Hypernova-Oy/lainuri/enclosures/KaskenPoltto.pdf

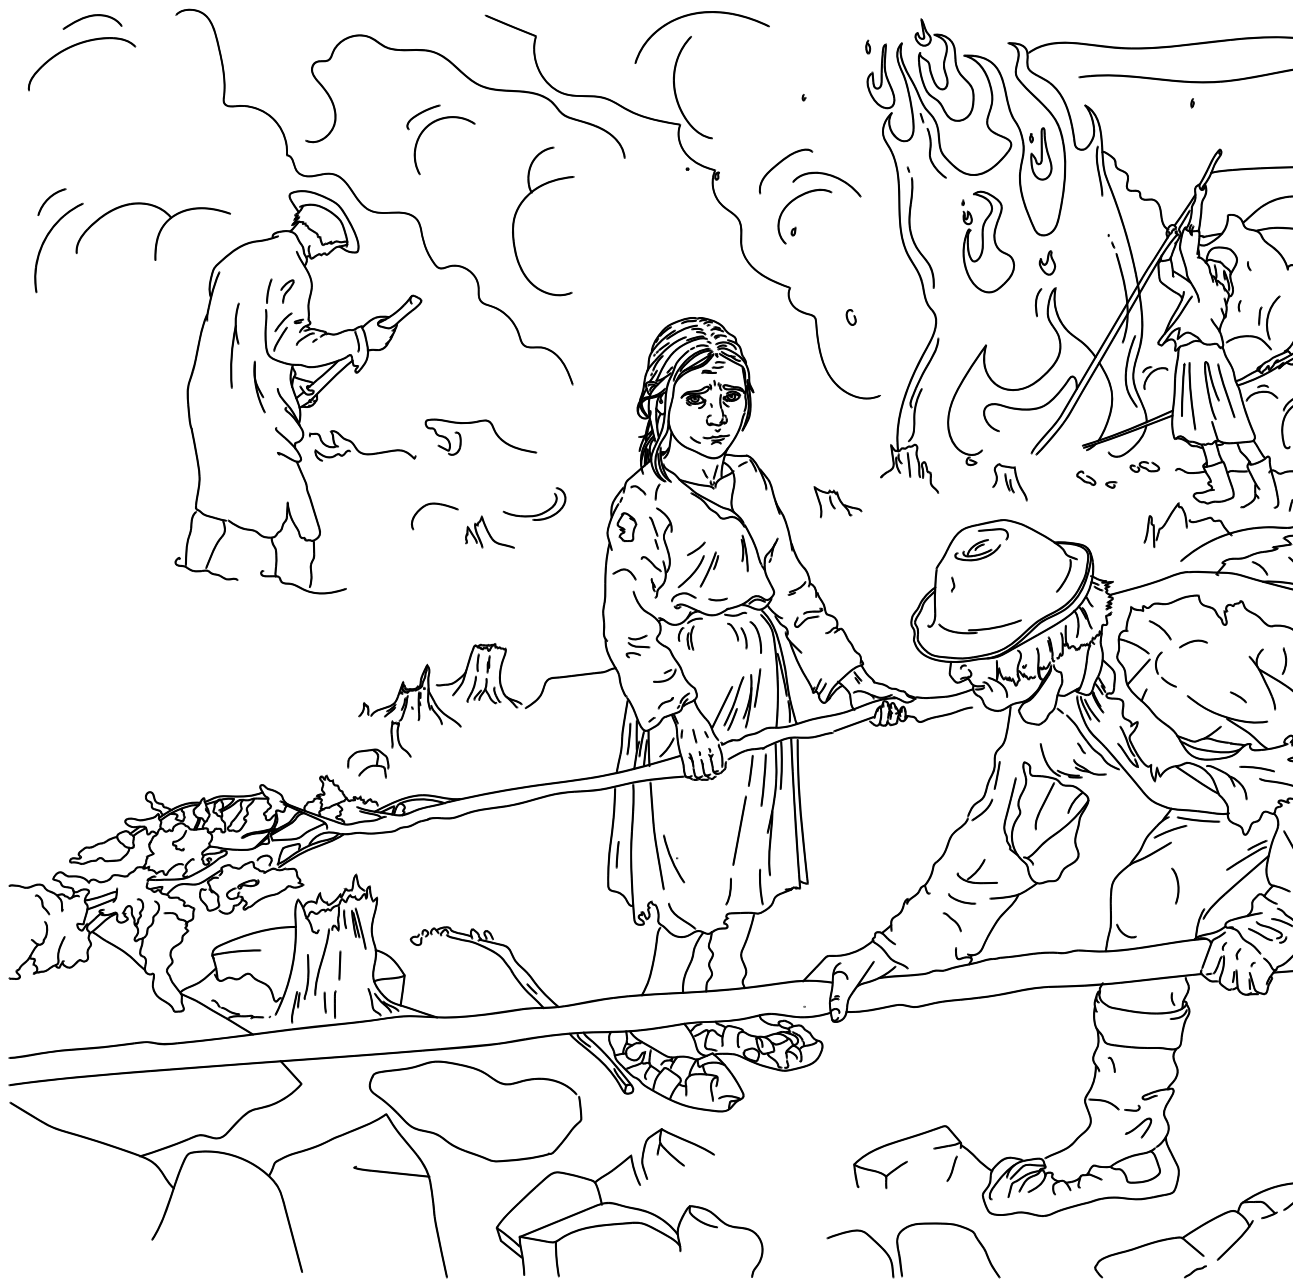
[picture p6: page 1]
