Hypernova-Oy/lainuri/enclosures/Lainuri-enclosure-4.5mm-art.pdf

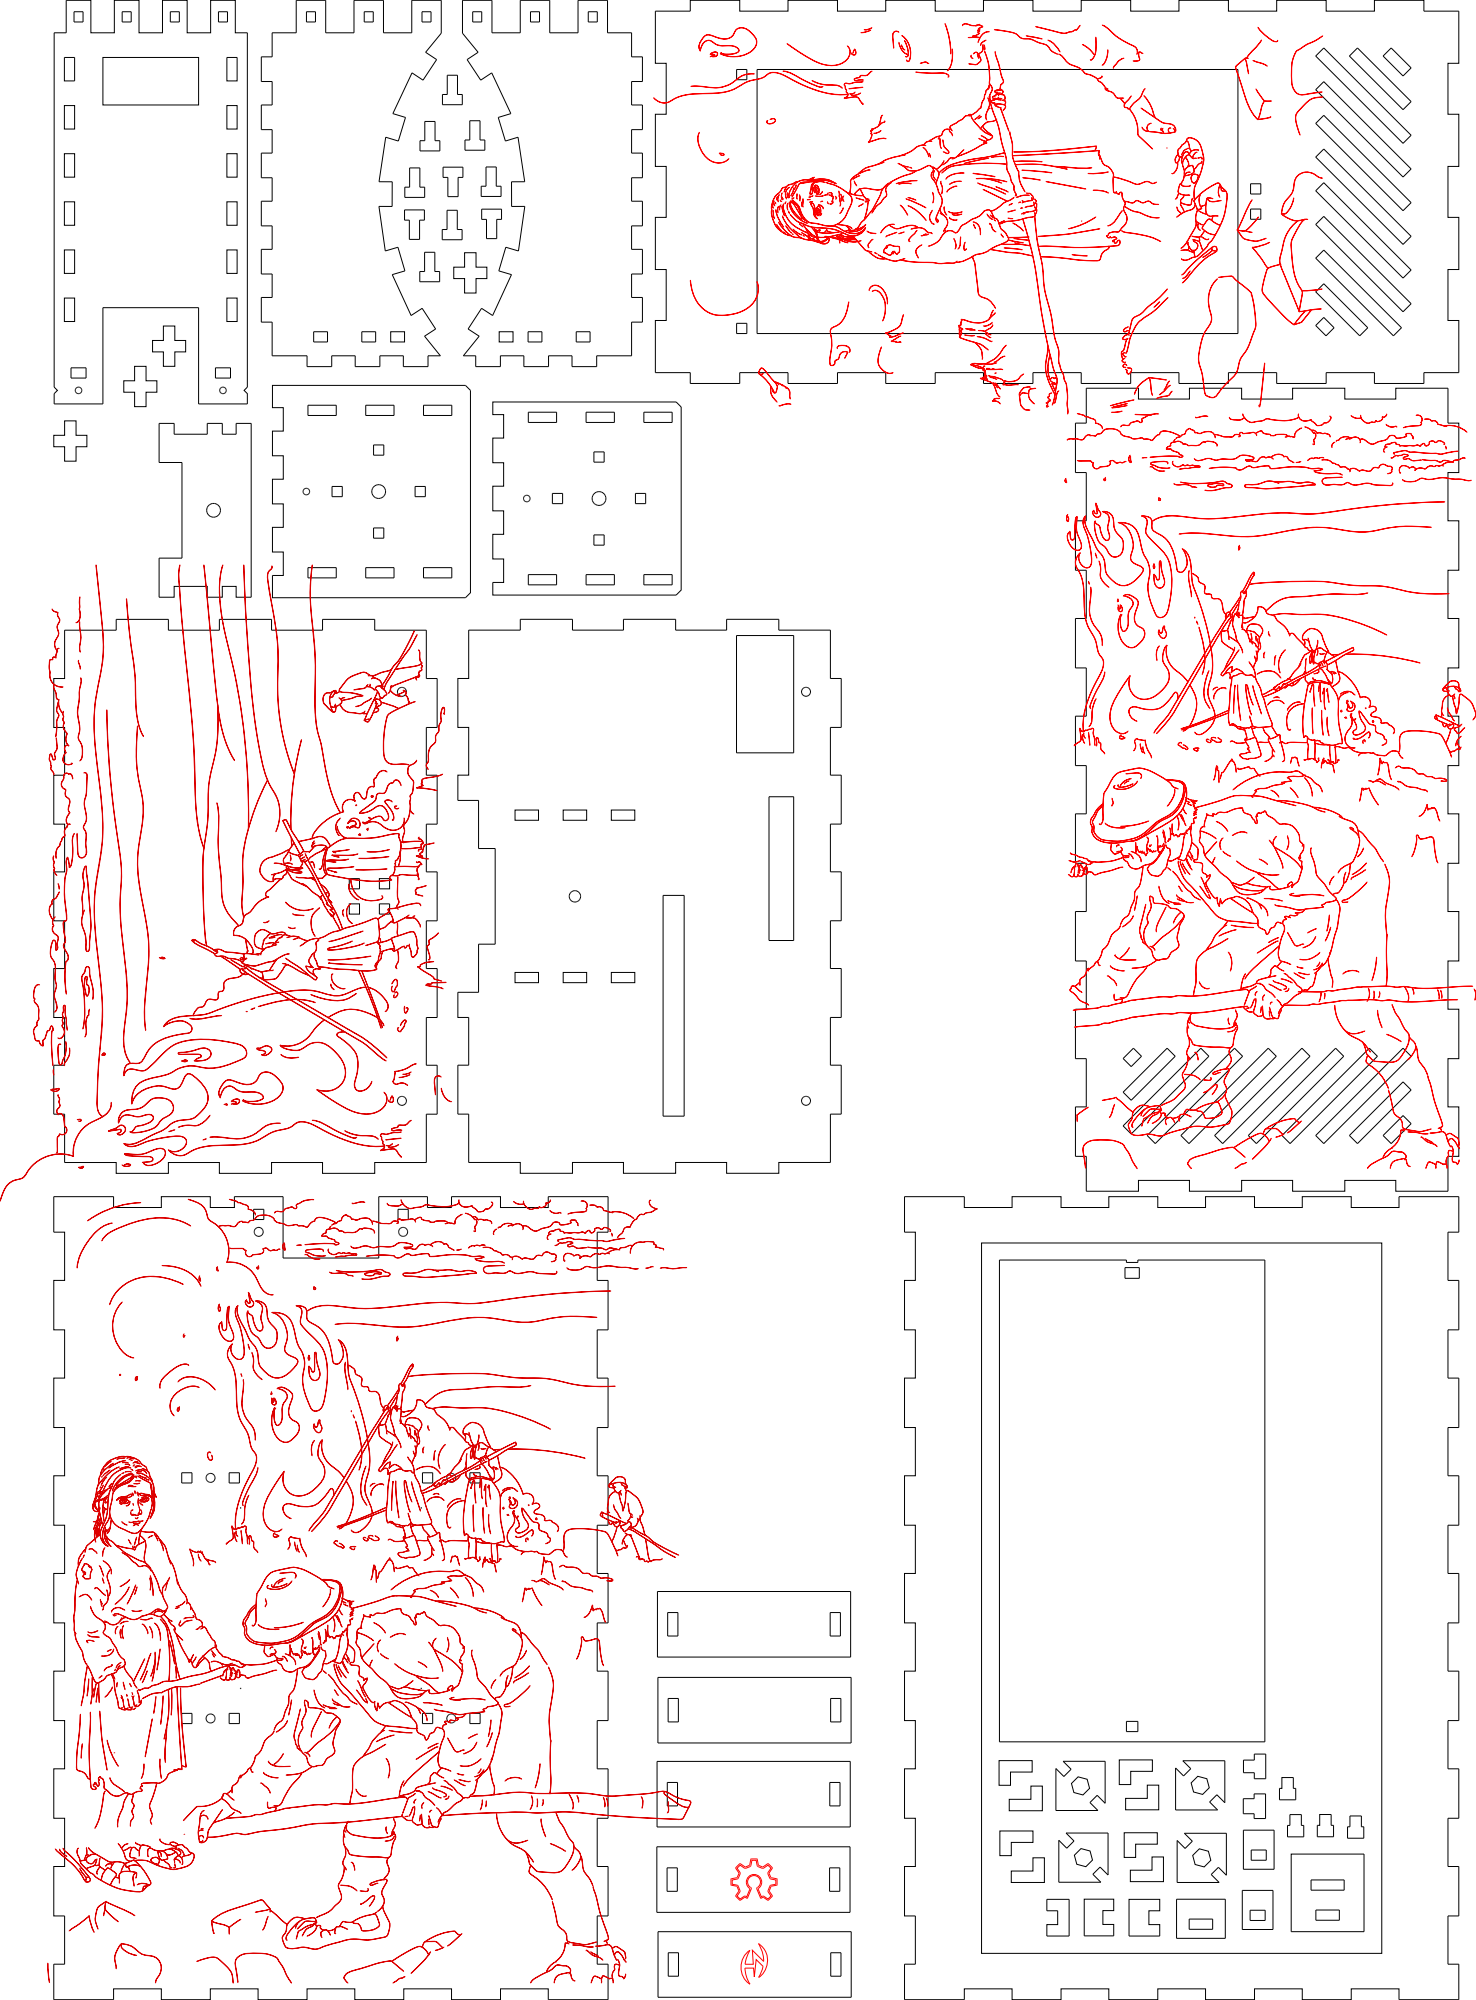
[picture p7: page 1]
