Hypernova-Oy/lainuri/programs/lainuri-serve/lainuri/printer.py

from lainuri.config import get_config, get_lainuri_conf_dir
from lainuri.logging_context import logging
log = logging.getLogger(__name__)

from lainuri.constants import Status
import lainuri.hs_k33
from lainuri.koha_api import koha_api
import lainuri.status

from jinja2 import Template
from datetime import datetime
import locale
import os
import time
import traceback
import weasyprint
import subprocess

cli_print_command = ['lp', '-']

def print_check_out_receipt(user_barcode: str, items: list):
  receipt_template = get_config('devices.thermal-printer.check-out-receipt')

  borrower = koha_api.get_borrower(user_barcode)

  printable_sheet = None
  if receipt_template.lower() == 'koha':
    printable_sheet = koha_api.receipt(borrower['borrowernumber'], 'qslip')
  else:
    printable_sheet = get_sheet(receipt_template, items, borrower)

  print_html(printable_sheet)
  return printable_sheet

def print_check_in_receipt(items: list, user_barcode: str = None):
  receipt_template = get_config('devices.thermal-printer.check-in-receipt')

  default_receipt_borrowernumber = get_config('devices.thermal-printer.check-in-receipt-koha-borrower')
  if user_barcode:
    borrower = koha_api.get_borrower(user_barcode=user_barcode)
  elif default_receipt_borrowernumber:
    borrower = koha_api.get_borrower(borrowernumber=get_config('devices.thermal-printer.check-in-receipt-koha-borrower'))
  else:
    borrower = {}

  printable_sheet = None
  if receipt_template.lower() == 'koha':
    if not borrower['borrowernumber']: raise TypeError("config('devices.thermal-printer.check-in-receipt') is 'koha', but there is no default borrower?")
    printable_sheet = koha_api.receipt(borrower['borrowernumber'], 'checkinslip')
  else:
    printable_sheet = get_sheet(receipt_template, items, borrower)

  print_html(printable_sheet)
  return printable_sheet

def print_html(html_text: str, page_increment: int = 10, css_dict: dict = None):
  """
  page_increment: Granularity to look for the minimum height of the document to fit all the content. the bigger the faster, but more paper is wasted with trailing margin.

  css_dict: Overload config.yaml's 'devices.thermal-printer.css' with this. Mostly useful for testing.
  """
  log.debug(f"print_html text='{html_text}'")
  try:
    _print_thermal_receipt(
      _prepare_weasy_doc(html_text=html_text, page_increment=page_increment, css_dict=css_dict)
    )
    lainuri.status.update_status('thermal_printer_status', Status.SUCCESS)
  except Exception as e:
    lainuri.status.update_status('thermal_printer_status', Status.ERROR)
    raise e
  return 1

def get_sheet(receipt_template_name: str, items: list, borrower: dict, header: str = None, footer: str = None) -> str:
  try:
    receipt_template = (get_lainuri_conf_dir() / receipt_template_name).read_text()
  except Exception as e:
    raise type(e)(e, f"Exception when get_sheet():> receipt template lookup path='{get_lainuri_conf_dir() / receipt_template_name}' get_lainuri_conf_dir() {get_lainuri_conf_dir()}, receipt_template_name '{receipt_template_name}'")
  return _render_jinja2_template(receipt_template=receipt_template, items=items, borrower=borrower, header=header, footer=footer)

def _prepare_weasy_doc(html_text: str, page_increment: int = 10, css_dict: dict = None) -> weasyprint.Document:
  doc = None
  start_time = time.time()

  weasy_html = weasyprint.HTML(string=html_text)

  pages = 256
  heigth = 20 # Keep looping to find the correct page size to fit all the content
  i = 0
  while pages != 1:
    i += 1
    default_css = weasyprint.CSS(string=' \
      body {\
        width: 72mm;\
        font-size: 12px;\
        margin: 0px;\
        padding: 0px;\
      }\
      @page {\
        size: 72mm '+str(heigth)+'mm;\
        margin: 0px;\
        padding: 0px;\
      }\
    ')
    doc = weasy_html.render(
      stylesheets=[default_css, *[weasyprint.CSS(string=css) for css in _format_css_rules_from_config(css_dict)]],
      enable_hinting = True,
      presentational_hints = True,
    )
    pages = len(doc.pages)

    # Simple heuristics to quickly detect the proper document length
    old_height = heigth
    if i == 1: heigth = heigth * (pages*0.9 if pages > 2 else pages)
    else: heigth = heigth + (page_increment * (pages-1))
    log.debug(f"Sampling to fit content on one document: i='{i}', old_height='{old_height}', pages='{pages}', new height='{heigth}'")

  end_time = time.time()
  log.info(f"print_html():> pages='{len(doc.pages)}', page_increment='{page_increment}px', html processing runtime='{end_time - start_time}s' iterations='{i}' page0='{doc.pages and doc.pages[0].__dict__}'")
  return doc

def _format_css_rules_from_config(css_dict: dict = None):
  if not css_dict: css_dict = get_config('devices.thermal-printer.css')
  if not css_dict: return []

  css = "body {\n"
  for css_directive, value in css_dict.items():
    if value[-1] != ';': value += ';'
    css += f"  {css_directive}: {value}\n"
  css += "}\n"

  css_string = get_config('devices.thermal-printer.css_string')
  return [stylesheet for stylesheet in [css, css_string] if stylesheet]

def _print_thermal_receipt(doc: weasyprint.Document):
  #TODO: Piloting ESC/POS raster image printing instead of using the rather slow and cumbersome CUPS. Using CUPS with ESC/POS might be impossible due to USB device congestion issues
  png_file_path = os.environ.get('LAINURI_LOG_DIR')+'/receipt.'+datetime.today().isoformat()+'.png'
  doc.write_png(target=png_file_path, resolution=203) # HS-K33 manual states the resolution to be 203 DPI
  _print_via_escpos_raster(png_file_path)
  #if (get_config('devices.thermal-printer.cups')):
  #  _print_via_cups(doc.to_pdf())

def _print_via_escpos_raster(png_file_path: str):
  printer = lainuri.hs_k33.get_printer()
  printer.escpos_printer.image(png_file_path, impl=u'bitImageRaster')
  printer.escpos_printer.cut()
  update_paper_status()

def update_paper_status():
  printer = lainuri.hs_k33.get_printer()
  ps = printer.paper_status()
  if ps == 2: lainuri.status.update_status('thermal_printer_paper_status') = Status.SUCCESS
  if ps == 1: lainuri.status.update_status('thermal_printer_paper_status') = Status.PENDING
  if ps == 0: lainuri.status.update_status('thermal_printer_paper_status') = Status.ERROR

def _print_via_cups(byttes: bytes):
  global cli_print_command
  ## Save to log the receipt document
  open(
    os.environ.get('LAINURI_LOG_DIR')+'/receipt.'+datetime.today().isoformat()+'.pdf',
    'wb',
  ).write(byttes)

  ## Invoke system CUPS printer
  if get_config('devices.thermal-printer.enabled'):
    process = subprocess.Popen(cli_print_command, stdout=subprocess.PIPE, stdin=subprocess.PIPE, stderr=subprocess.PIPE)
    process.communicate(input=byttes, timeout=20)
    if process.returncode != 0:
      raise Exception(f"Program exit code not 0. exit='{process.returncode}', stderr='{process.stderr}', stdout='{process.stdout}', command='{cli_print_command}'")

  else:
    log.info(f"Thermal printer is disabled from configuration.")

def _render_jinja2_template(receipt_template: str, items: list, borrower: dict, header: str = None, footer: str = None):
  return Template(receipt_template).render(
    items=items,
    borrower=borrower,
    today=datetime.today().strftime(locale.nl_langinfo(locale.D_FMT) + ' ' + locale.nl_langinfo(locale.T_FMT)),
    header=header,
    footer=footer,
  )
