Hypernova-Oy/lainuri/programs/lainuri-serve/bin/rtttl_player.py

import sys
sys.path.insert(0, __file__+'/../..')

import lainuri.rtttl_player as rtttl

lainuri.rtttl_player.play_rtttl("Axelf:d=8,o=5,b=160:4f#,a.,f#,16f#,a#,f#,e,4f#,c6.,f#,16f#,d6,c#6,a,f#,c#6,f#6,16f#,e,16e,c#,g#,4f#.")
